starfleetbio/Geodesic/tests/dev/Test_7_Panels/T4_GR.3mf

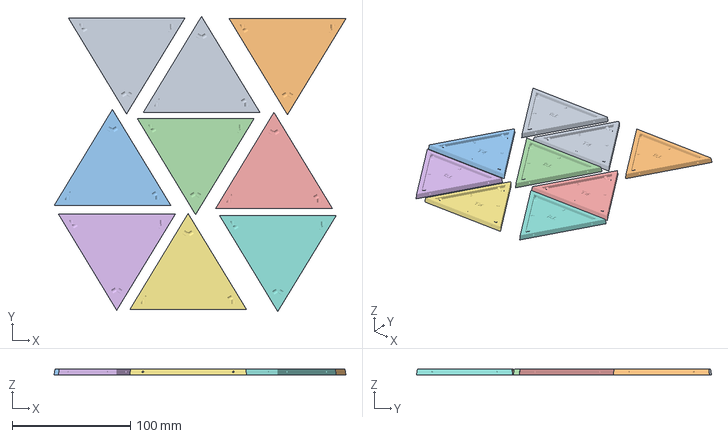
[picture p29: CAD file, 2026-09-07]
tests/dev/Test_7_Panels/T4_GR.3mf
247.4 x 250.2 x 5.11 mm
T4.stl x 9
