starfleetbio/Geodesic/stl/T5.stl

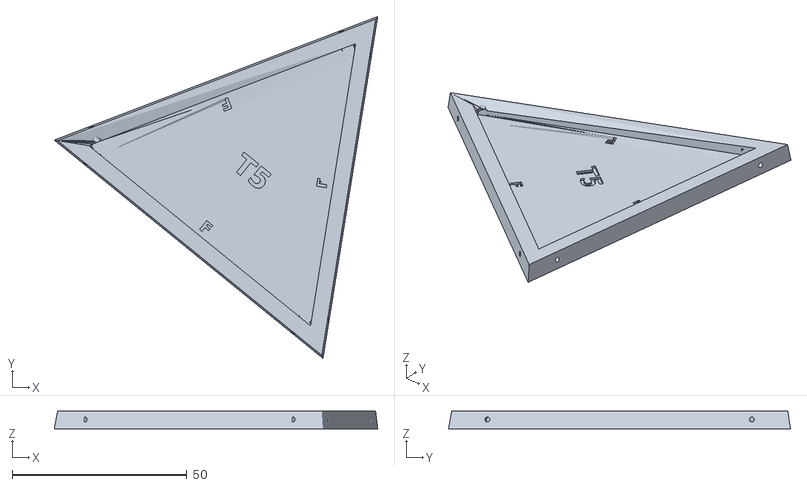
[picture p30: CAD file, 2026-09-12]
stl/T5.stl
92.6 x 97.9 x 5.11
