starfleetbio/Geodesic/tests/dev/Test_1_Panels/FACE_p2.stl

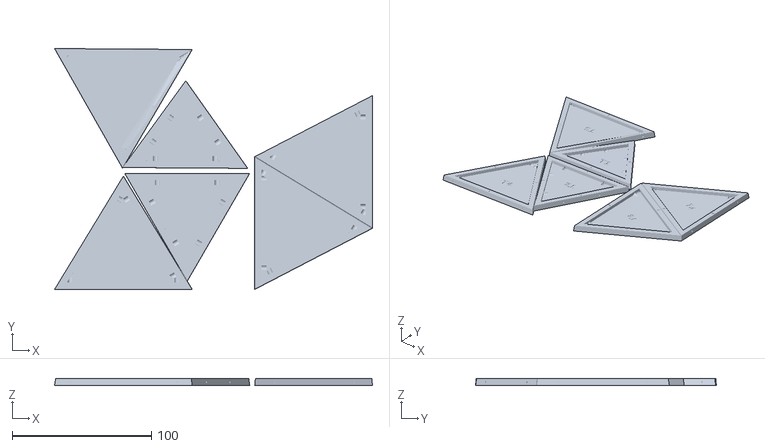
[picture p31: CAD file, 2026-08-19]
tests/dev/Test_1_Panels/FACE_p2.stl
228.6 x 173.2 x 5.34
