starfleetbio/Geodesic/tests/dev/Test_1_Panels/singles/T2.stl

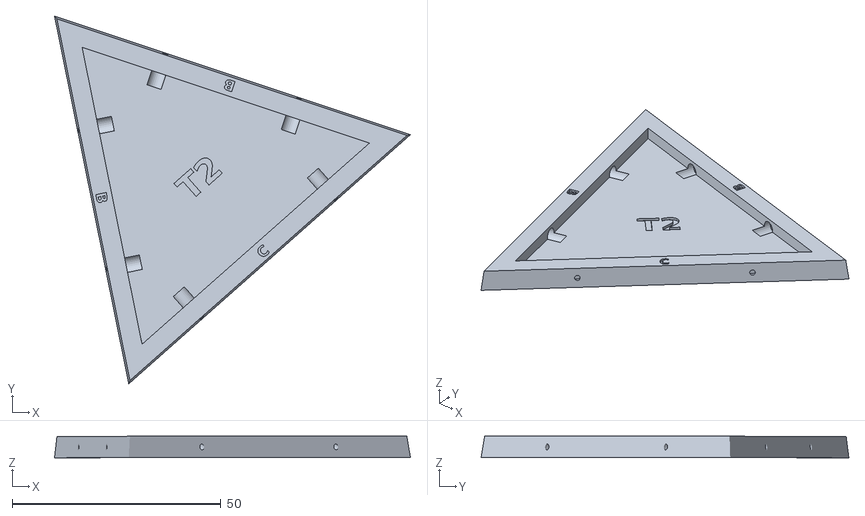
[picture p32: CAD file, 2026-08-19]
tests/dev/Test_1_Panels/singles/T2.stl
85.2 x 88.1 x 5.16
