starfleetbio/Geodesic/tests/dev/Test_1_Panels/Test/Test_4v_plate_2.3mf

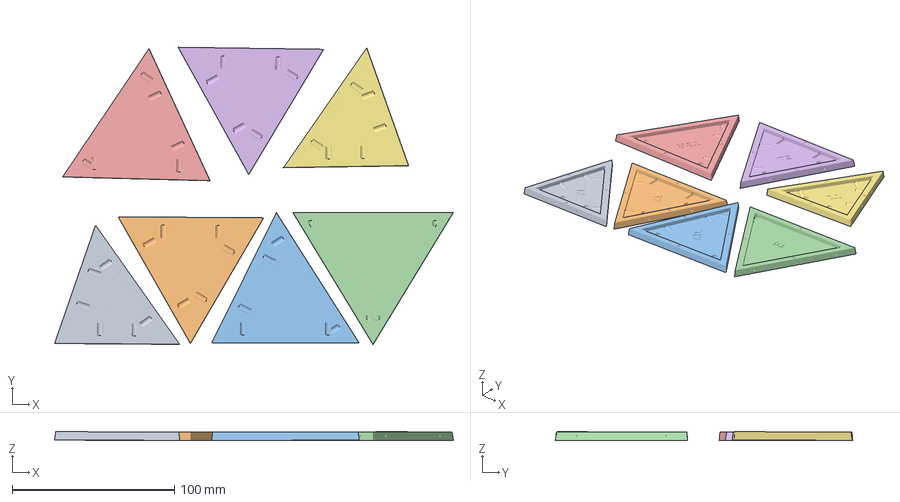
[picture p33: CAD file, 2026-08-19]
tests/dev/Test_1_Panels/Test/Test_4v_plate_2.3mf
245.9 x 183.3 x 5.35 mm
T1.stl x 2
T2.stl x 2
T3L.stl
T4.stl
T3R.stl
