starfleetbio/Geodesic/tests/dev/Test_2_Panels/FACE_p1.stl

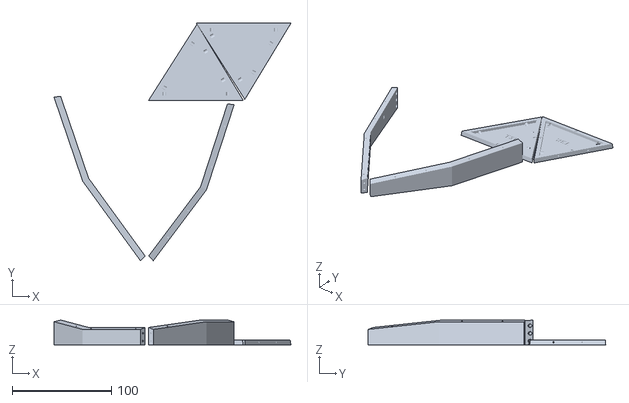
[picture p34: CAD file, 2026-08-19]
tests/dev/Test_2_Panels/FACE_p1.stl
238.9 x 239.5 x 25.2
