starfleetbio/Geodesic/tests/dev/Test_2_Panels/singles/throat_coupon2_T1.stl

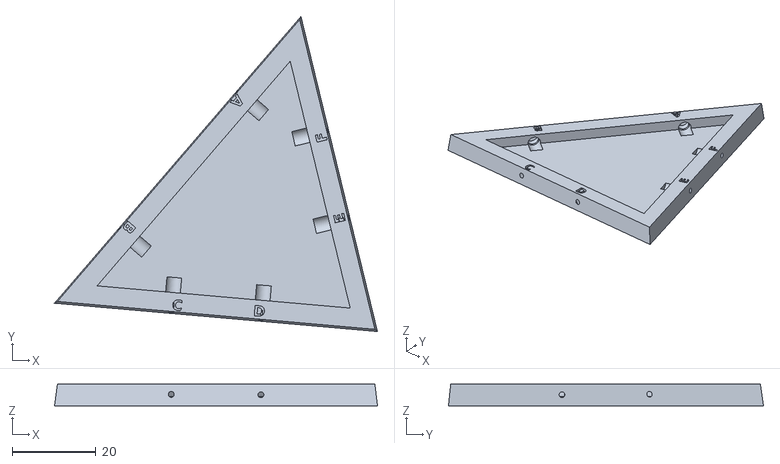
[picture p35: CAD file, 2026-08-31]
tests/dev/Test_2_Panels/singles/throat_coupon2_T1.stl
76.9 x 75.0 x 5.14
