starfleetbio/Geodesic/tests/dev/Test_2_Panels/Test/throat_coupon2_T1.3mf

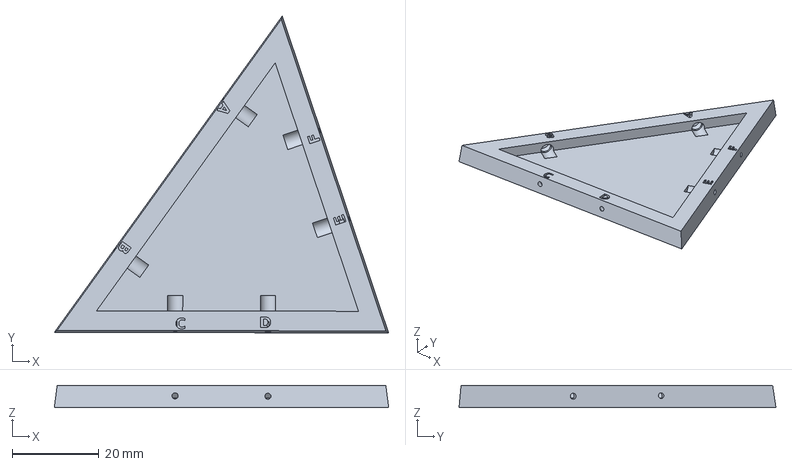
[picture p36: CAD file, 2026-08-31]
tests/dev/Test_2_Panels/Test/throat_coupon2_T1.3mf
77.2 x 73.2 x 5.14 mm
