starfleetbio/Geodesic/tests/dev/Test_3_Arcs/arc_F_piece.stl

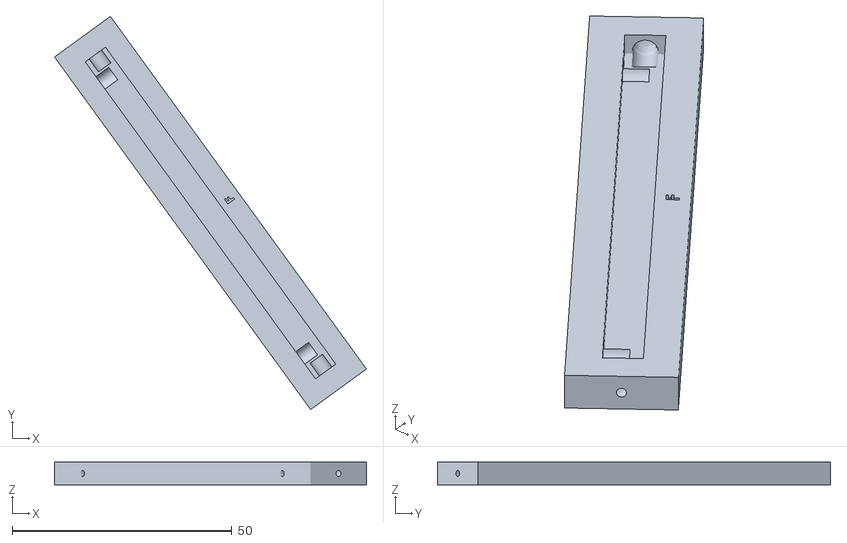
[picture p37: CAD file, 2026-08-31]
tests/dev/Test_3_Arcs/arc_F_piece.stl
71.0 x 89.4 x 5.20
