starfleetbio/Geodesic/tests/dev/Test_4_Arcs/singles/arc_run_BR.stl

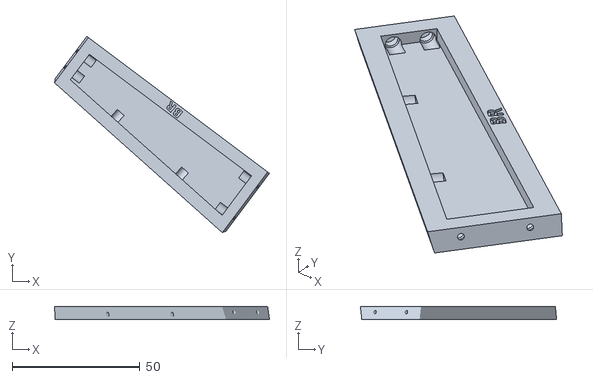
[picture p38: CAD file, 2026-08-31]
tests/dev/Test_4_Arcs/singles/arc_run_BR.stl
84.3 x 76.9 x 4.96
