starfleetbio/Geodesic/tests/dev/Test_6_Arcs_Panels/arc_T2.stl

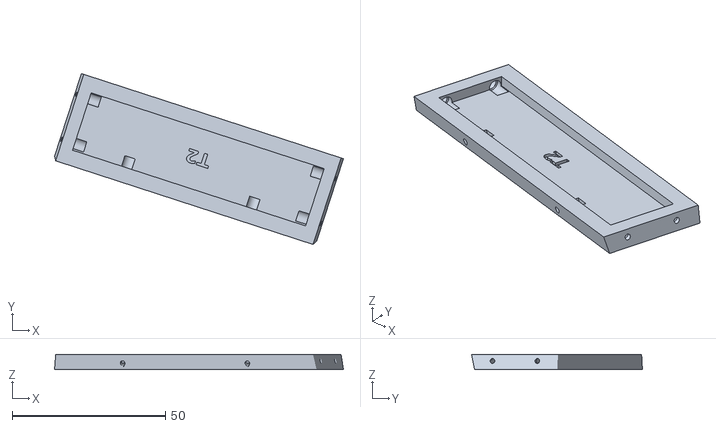
[picture p39: CAD file, 2026-09-02]
tests/dev/Test_6_Arcs_Panels/arc_T2.stl
94.4 x 55.8 x 4.97
