starfleetbio/Geodesic/stl/T3L.stl

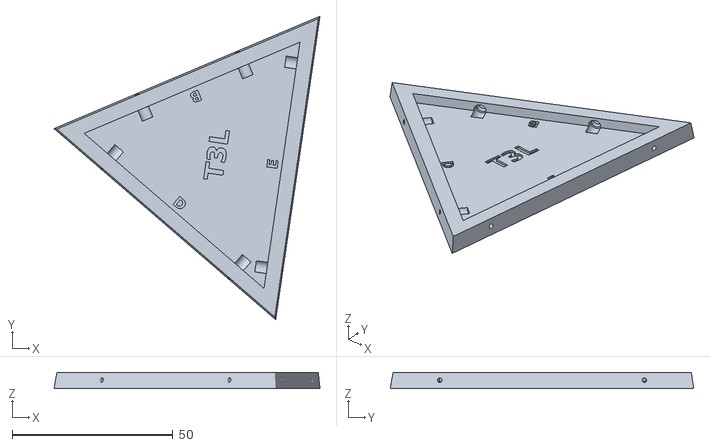
[picture p40: CAD file, 2026-09-02]
stl/T3L.stl
82.8 x 94.4 x 5.12
