starfleetbio/Geodesic/tests/3mf/T5_DK_GR.3mf

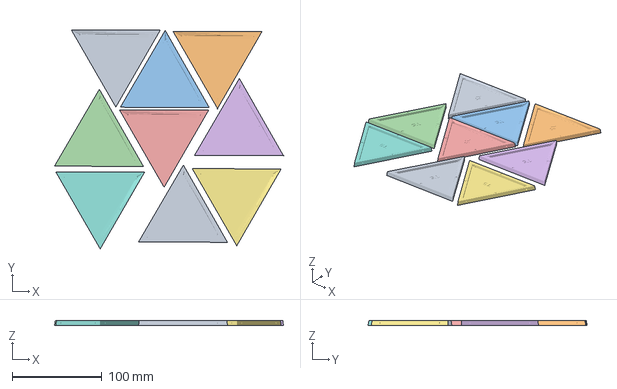
[picture p41: CAD file, 2026-08-31]
tests/3mf/T5_DK_GR.3mf
255.1 x 243.8 x 5.11 mm
T5.stl x 9
