starfleetbio/Geodesic/tests/dev/Test_1_Panels/FACE_p3.stl

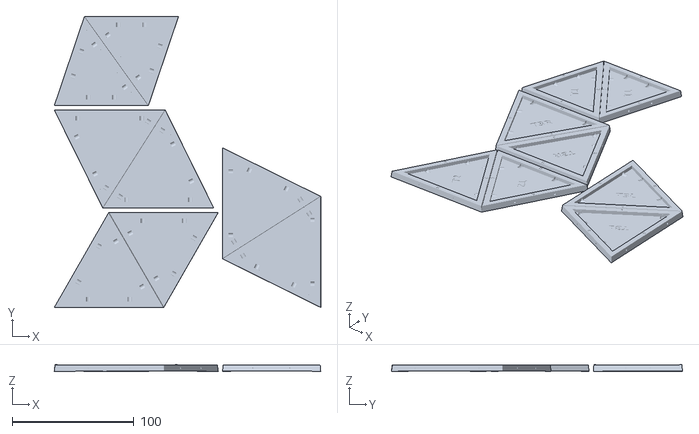
[picture p42: CAD file, 2026-08-19]
tests/dev/Test_1_Panels/FACE_p3.stl
218.5 x 238.6 x 5.34
