starfleetbio/Geodesic/tests/dev/Test_2_Panels/FACE_p3.stl

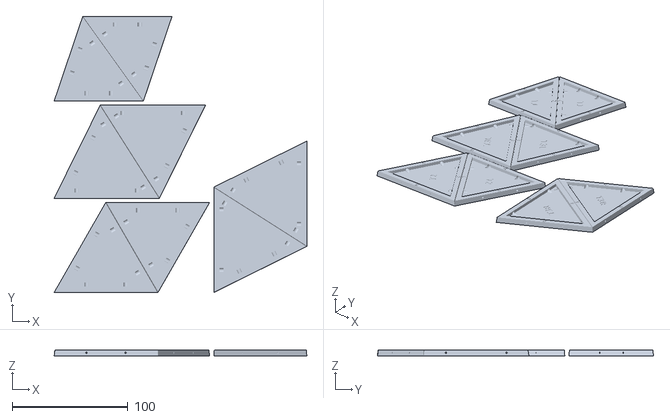
[picture p43: CAD file, 2026-08-19]
tests/dev/Test_2_Panels/FACE_p3.stl
218.5 x 238.6 x 5.14
