starfleetbio/Geodesic/tests/dev/Test_2_Panels/singles/error/T4.stl

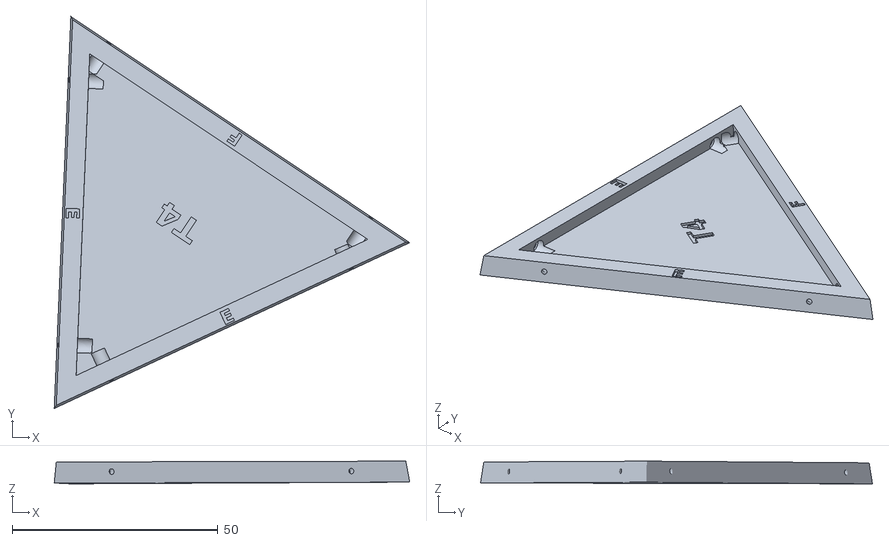
[picture p44: CAD file, 2026-08-19]
tests/dev/Test_2_Panels/singles/error/T4.stl
86.5 x 95.3 x 5.53
