starfleetbio/Geodesic/tests/dev/Test_2_Panels/Test/Test_4v_plate_2.3mf

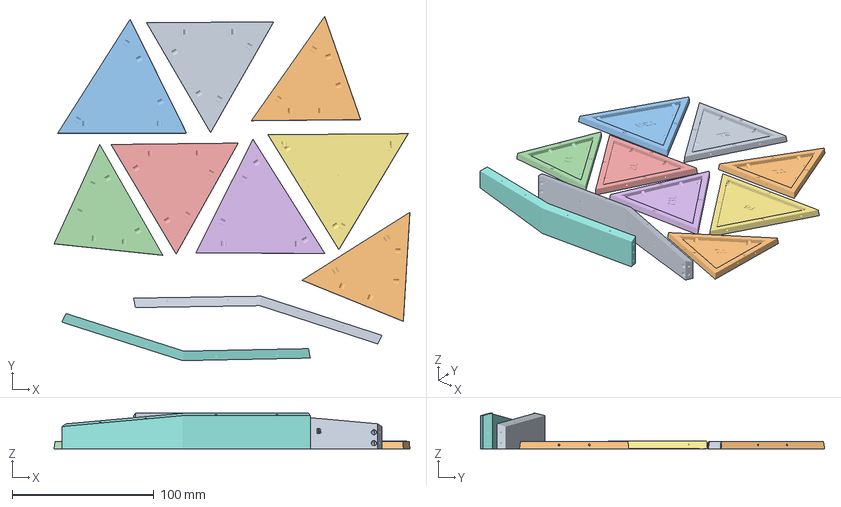
[picture p45: CAD file, 2026-08-19]
tests/dev/Test_2_Panels/Test/Test_4v_plate_2.3mf
251.1 x 242.8 x 25.2 mm
T2.stl x 2
T1.stl x 3
T3R.stl
T3L.stl
T4.stl
arcT2T3.stl x 2
