starfleetbio/Geodesic/tests/dev/Test_3_Arcs/arc_C_piece.stl

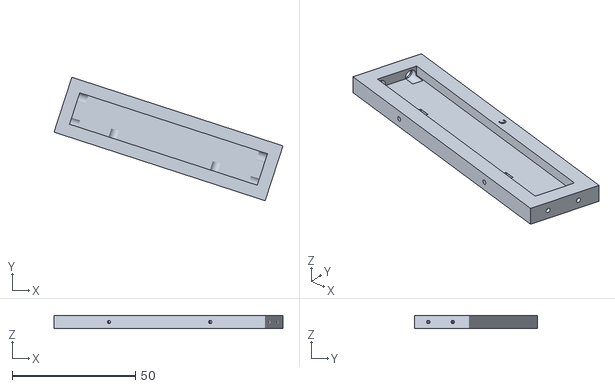
[picture p46: CAD file, 2026-08-31]
tests/dev/Test_3_Arcs/arc_C_piece.stl
92.9 x 50.1 x 5.20
