starfleetbio/Geodesic/tests/dev/Test_5_Arcs/T3R_t30.stl

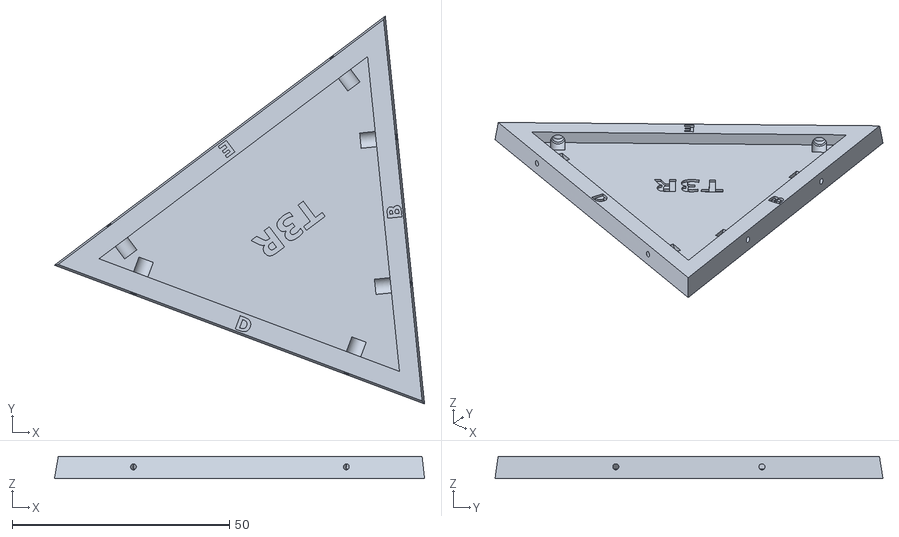
[picture p47: CAD file, 2026-09-02]
tests/dev/Test_5_Arcs/T3R_t30.stl
85.3 x 89.4 x 5.12
