starfleetbio/Geodesic/tests/dev/Test_7_Panels/T1_JADE.3mf

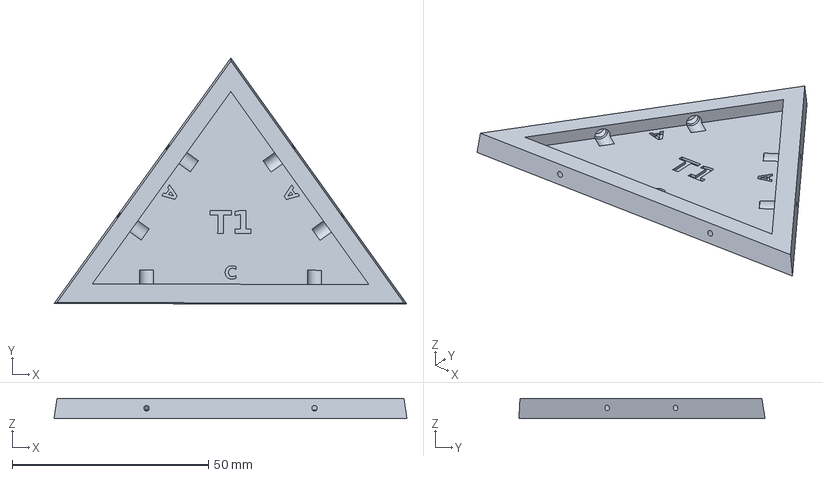
[picture p48: CAD file, 2026-09-07]
tests/dev/Test_7_Panels/T1_JADE.3mf
90.0 x 62.8 x 5.14 mm
