starfleetbio/Geodesic/3mf/T3R_SILVER_4X.3mf

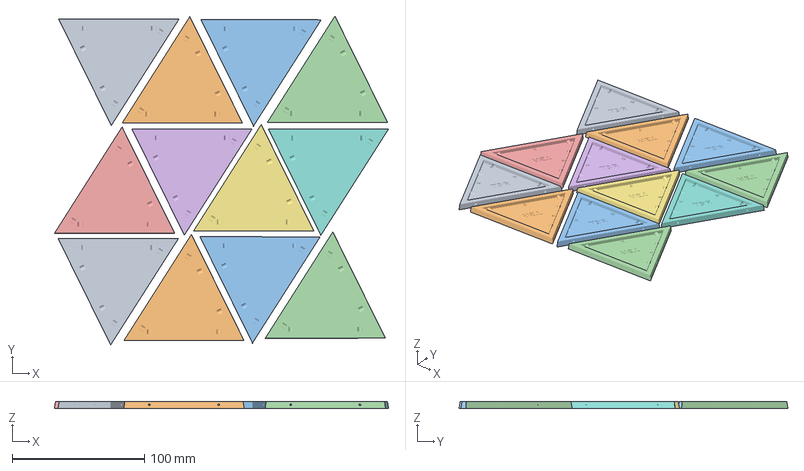
[picture p49: CAD file, 2026-09-12]
3mf/T3R_SILVER_4X.3mf
252.8 x 248.9 x 5.12 mm
T3R.stl x 12
