starfleetbio/Geodesic/stl/T2.stl

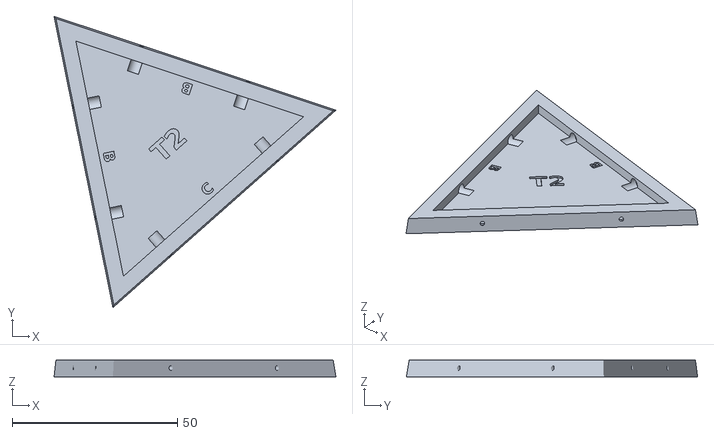
[picture p50: CAD file, 2026-09-02]
stl/T2.stl
85.2 x 88.0 x 5.12
