starfleetbio/Geodesic/tests/dev/Test_1_Panels/singles/arcT2T3.stl

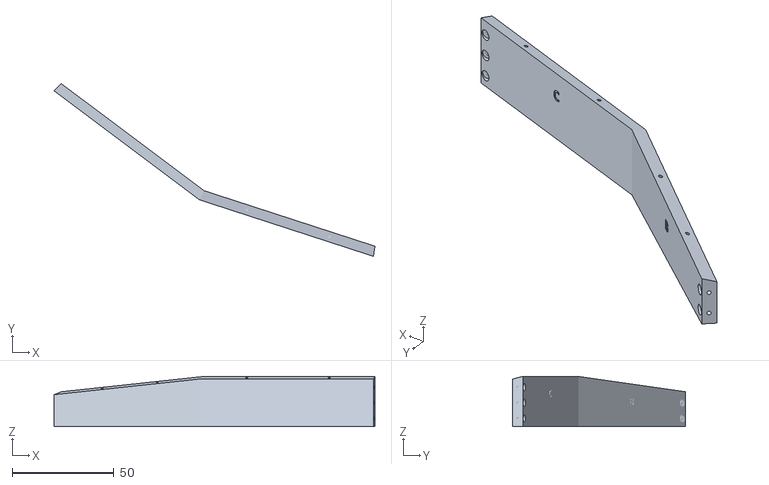
[picture p51: CAD file, 2026-08-19]
tests/dev/Test_1_Panels/singles/arcT2T3.stl
158.0 x 85.0 x 24.7
