starfleetbio/Geodesic/tests/dev/Test_2_Panels/singles/error/T5.stl

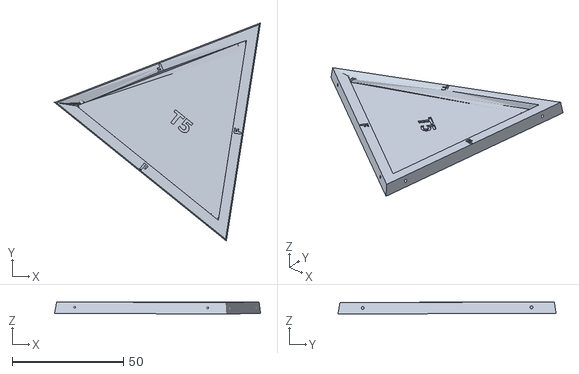
[picture p52: CAD file, 2026-08-19]
tests/dev/Test_2_Panels/singles/error/T5.stl
92.5 x 97.9 x 5.41
