starfleetbio/Geodesic/tests/dev/Test_3_Arcs/arc_BL_piece.stl

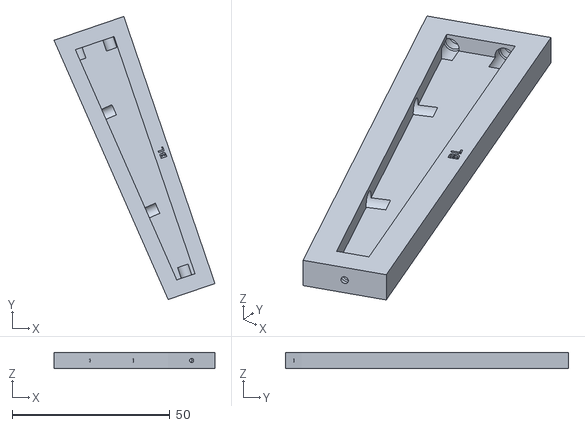
[picture p53: CAD file, 2026-08-31]
tests/dev/Test_3_Arcs/arc_BL_piece.stl
51.1 x 89.8 x 5.20
