starfleetbio/Geodesic/tests/dev/Test_4_Arcs/singles/arc_run_F.stl

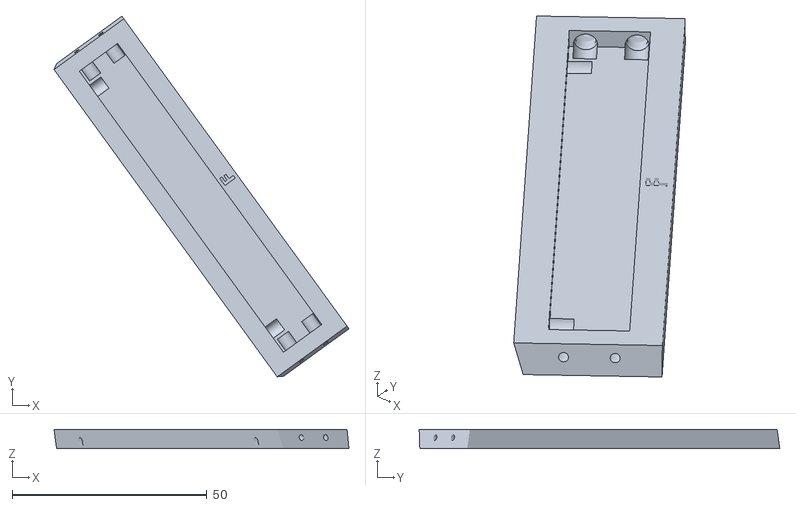
[picture p54: CAD file, 2026-08-31]
tests/dev/Test_4_Arcs/singles/arc_run_F.stl
75.7 x 92.5 x 4.93
