starfleetbio/Geodesic/tests/dev/Test_5_Arcs/T3L_T3R_SILVER.3mf

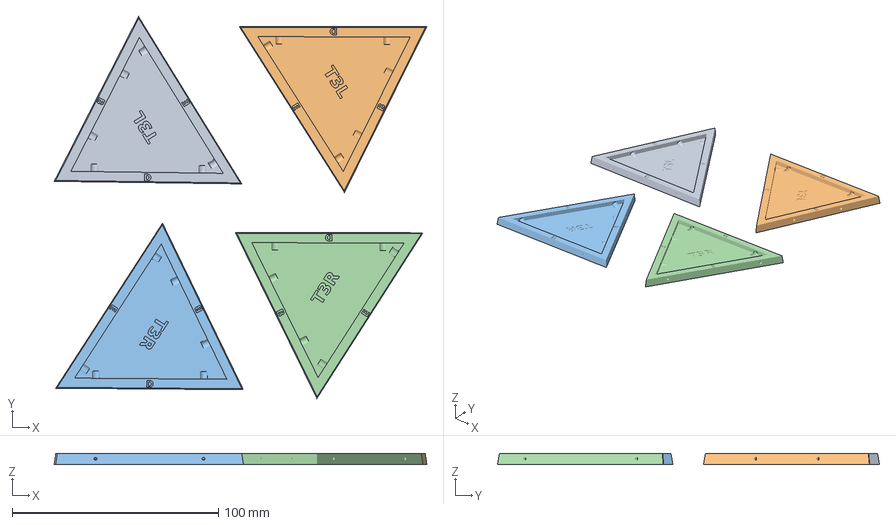
[picture p55: CAD file, 2026-09-02]
tests/dev/Test_5_Arcs/T3L_T3R_SILVER.3mf
180.8 x 185.3 x 5.12 mm
T3L_t30.stl x 2
T3R_t30.stl x 2
