starfleetbio/Geodesic/tests/dev/Test_6_Arcs_Panels/arc_BLK.3mf

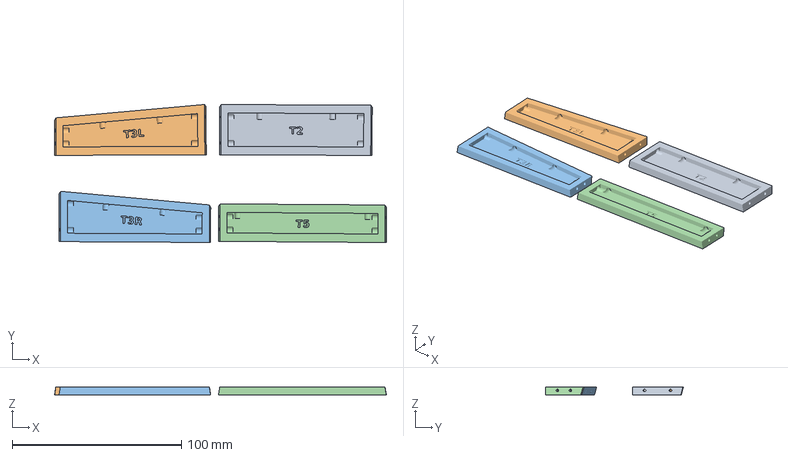
[picture p56: CAD file, 2026-09-02]
tests/dev/Test_6_Arcs_Panels/arc_BLK.3mf
195.9 x 81.5 x 4.97 mm
arc_T2.stl
arc_T3L.stl
arc_T3R.stl
arc_T5.stl
