starfleetbio/Geodesic/tests/dev/Test_1_Panels/singles/T1.stl

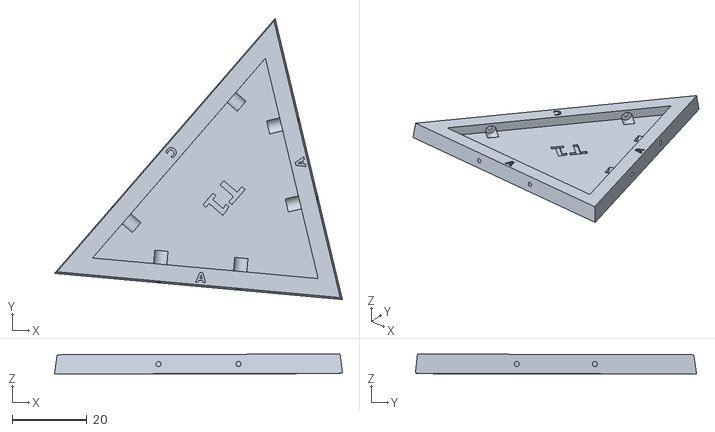
[picture p57: CAD file, 2026-08-19]
tests/dev/Test_1_Panels/singles/T1.stl
76.9 x 75.1 x 5.34
