starfleetbio/Geodesic/tests/dev/Test_5_Arcs/T2_LT_GR.3mf

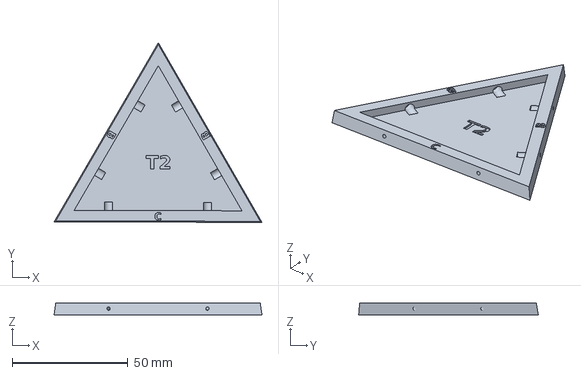
[picture p58: CAD file, 2026-09-02]
tests/dev/Test_5_Arcs/T2_LT_GR.3mf
90.0 x 77.8 x 5.12 mm
