starfleetbio/Geodesic/3mf/T1_JADE_3X.3mf

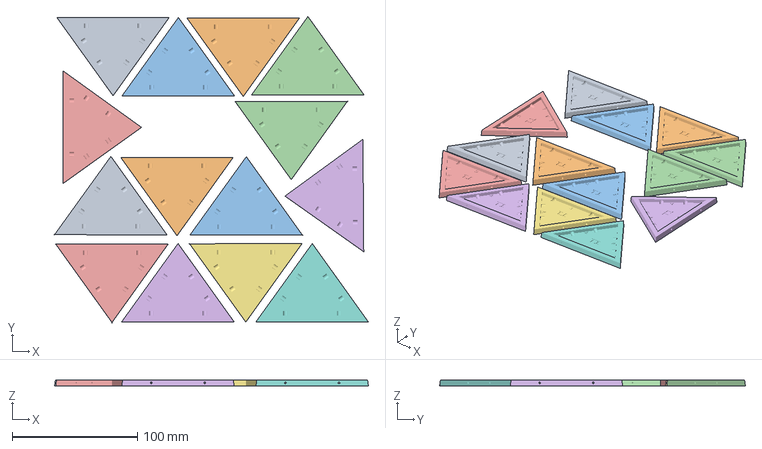
[picture p59: CAD file, 2026-09-11]
3mf/T1_JADE_3X.3mf
251.1 x 244.8 x 5.14 mm
T1.stl x 14
