starfleetbio/Geodesic/tests/dev/Test_1_Panels/singles/T3L.stl

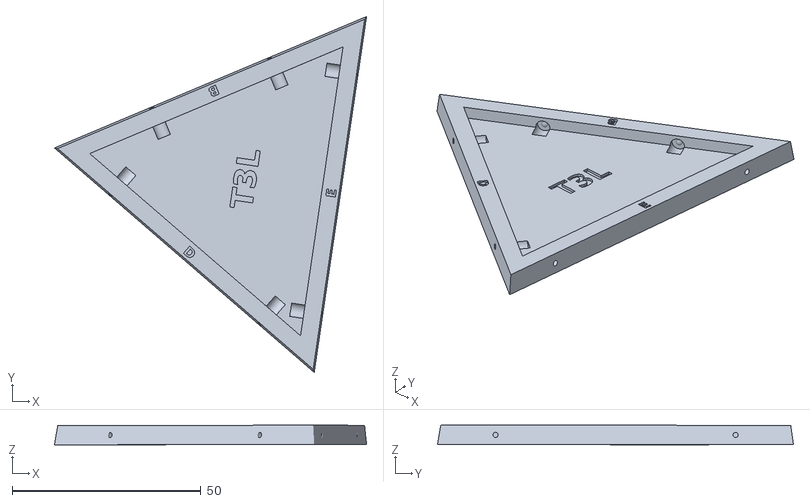
[picture p60: CAD file, 2026-08-19]
tests/dev/Test_1_Panels/singles/T3L.stl
82.8 x 94.4 x 5.22
