starfleetbio/Geodesic/tests/dev/Test_1_Panels/singles/T3R.stl

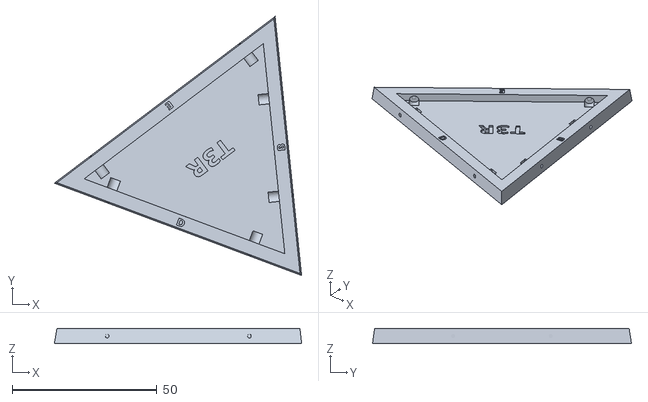
[picture p61: CAD file, 2026-08-19]
tests/dev/Test_1_Panels/singles/T3R.stl
85.3 x 89.4 x 5.22
