starfleetbio/Geodesic/tests/dev/Test_2_Panels/singles/arcT2T3.stl

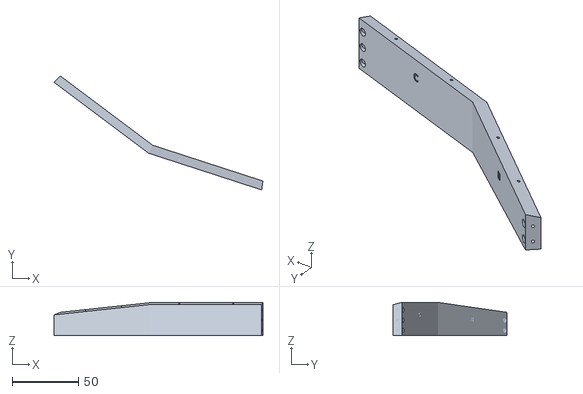
[picture p62: CAD file, 2026-08-19]
tests/dev/Test_2_Panels/singles/arcT2T3.stl
158.3 x 86.2 x 25.2
