starfleetbio/Geodesic/tests/3mf/arc_BLK.3mf

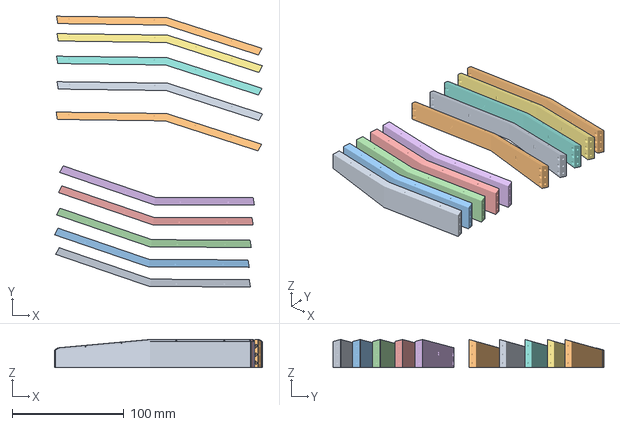
[picture p63: CAD file, 2026-08-31]
tests/3mf/arc_BLK.3mf
186.5 x 242.7 x 25.2 mm
arcT2T3.stl x 5
arcT5T3.stl x 5
