starfleetbio/Geodesic/tests/dev/Test_1_Panels/singles/arcT5T3.stl

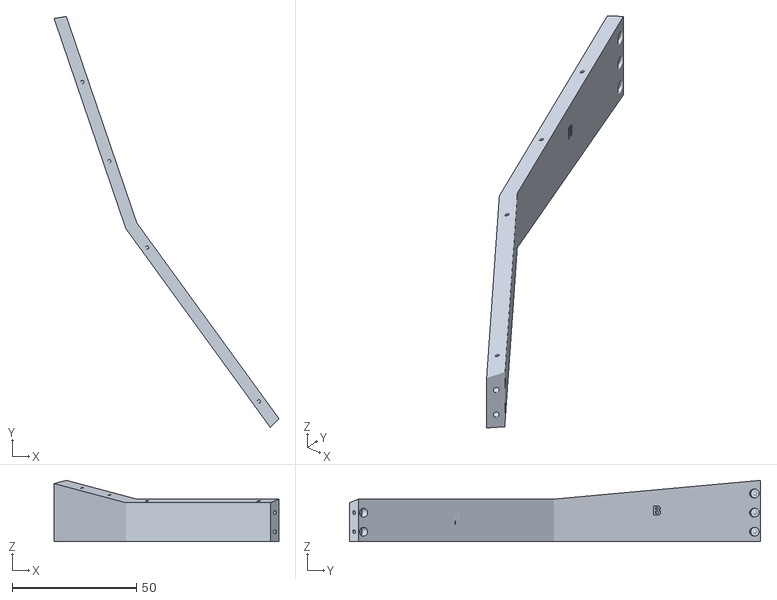
[picture p64: CAD file, 2026-08-19]
tests/dev/Test_1_Panels/singles/arcT5T3.stl
90.7 x 165.6 x 24.7
