starfleetbio/Geodesic/tests/dev/Test_5_Arcs/T5_DK_GR.3mf

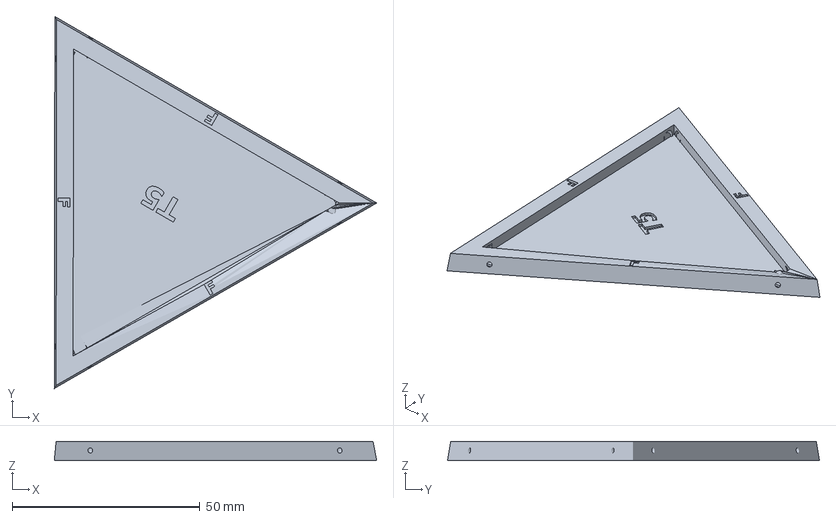
[picture p65: CAD file, 2026-09-02]
tests/dev/Test_5_Arcs/T5_DK_GR.3mf
85.9 x 99.1 x 5.11 mm
