starfleetbio/Geodesic/tests/dev/Test_2_Panels/singles/arcT5T3.stl

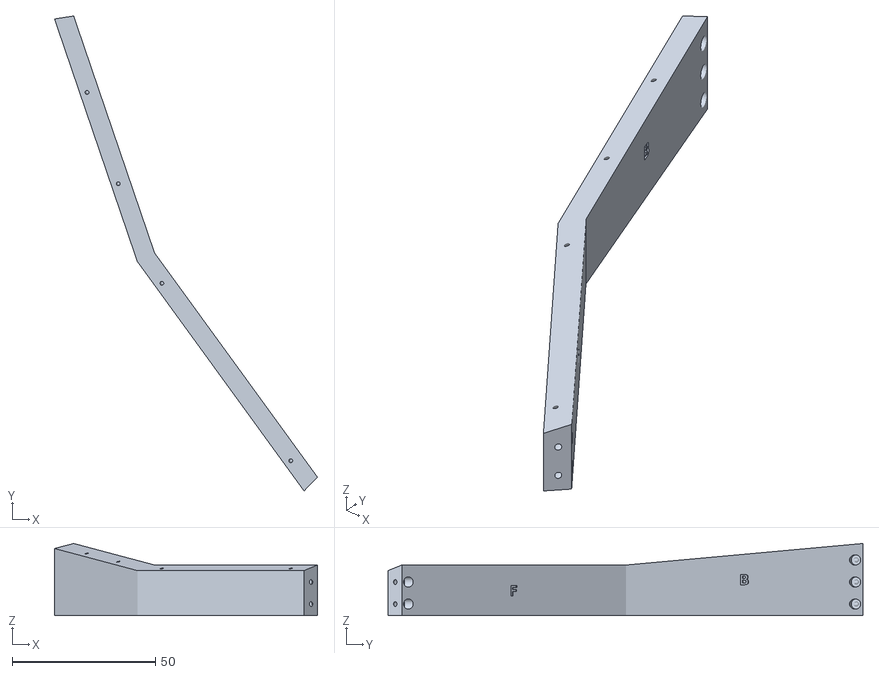
[picture p66: CAD file, 2026-08-19]
tests/dev/Test_2_Panels/singles/arcT5T3.stl
91.9 x 165.9 x 25.2
